joshr120/open-deck/Code/Arduino/macro_keyboard_with_MQTT/bitmap.h

//Custom Bitmaps:

//Image colours are stored seperatly these are just the bitmaps


unsigned char chrome_r [] = {
  0x00, 0x00, 0x00, 0x00, 0x00, 0x00, 0x00, 
0x00, 0x00, 0x00, 0x00, 0x00, 0x00, 0x00, 
0x00, 0x00, 0x00, 0x00, 0x00, 0x00, 0x00, 
0x00, 0x00, 0x00, 0x00, 0x00, 0x00, 0x00, 
0x00, 0x00, 0x00, 0x00, 0x00, 0x00, 0x00, 
0x00, 0x00, 0x00, 0x00, 0x00, 0x00, 0x00, 
0x00, 0x00, 0x00, 0x00, 0x00, 0x00, 0x00, 
0x00, 0x00, 0x00, 0x00, 0x00, 0x00, 0x00, 
0x00, 0x00, 0x00, 0x00, 0x00, 0x00, 0x00, 
0x00, 0x00, 0x01, 0xfe, 0x00, 0x00, 0x00, 
0x00, 0x00, 0x3f, 0xff, 0xe0, 0x00, 0x00, 
0x00, 0x00, 0xff, 0xff, 0xfc, 0x00, 0x00, 
0x00, 0x03, 0xff, 0xff, 0xfe, 0x00, 0x00, 
0x00, 0x0f, 0xff, 0xff, 0xff, 0x80, 0x00, 
0x00, 0x1f, 0xff, 0xff, 0xff, 0xc0, 0x00, 
0x00, 0x3f, 0xff, 0xff, 0xff, 0xf0, 0x00, 
0x00, 0x7f, 0xff, 0xff, 0xff, 0xf8, 0x00, 
0x01, 0xff, 0xff, 0xff, 0xff, 0xfc, 0x00, 
0x01, 0xff, 0xff, 0xff, 0xff, 0xfc, 0x00, 
0x01, 0xff, 0xff, 0xff, 0xff, 0xfe, 0x00, 
0x01, 0xff, 0xff, 0xff, 0xff, 0xff, 0x00, 
0x00, 0xff, 0xff, 0xff, 0xff, 0xff, 0x80, 
0x00, 0x7f, 0xff, 0xff, 0xff, 0xff, 0x80, 
0x00, 0x7f, 0xff, 0xff, 0xff, 0xff, 0x80, 
0x00, 0x3f, 0xfc, 0x00, 0x00, 0x00, 0x00, 
0x00, 0x3f, 0xf0, 0x00, 0x00, 0x00, 0x00, 
0x00, 0x1f, 0xe0, 0x00, 0x00, 0x00, 0x00, 
0x00, 0x0f, 0xc0, 0x00, 0x00, 0x00, 0x00, 
0x00, 0x0f, 0x80, 0x00, 0x00, 0x00, 0x00, 
0x00, 0x07, 0x80, 0x00, 0x00, 0x00, 0x00, 
0x00, 0x07, 0x00, 0x00, 0x00, 0x00, 0x00, 
0x00, 0x03, 0x00, 0x00, 0x00, 0x00, 0x00, 
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
0x00, 0x00, 0x00, 0x00, 0x03, 0xff, 0xf0, 
0x00, 0x00, 0x00, 0x00, 0x03, 0xff, 0xf0, 
0x00, 0x00, 0x00, 0x00, 0x03, 0xff, 0xf0, 
0x00, 0x00, 0x00, 0x00, 0x03, 0xff, 0xf0, 
0x00, 0x00, 0x00, 0x00, 0x03, 0xff, 0xf0, 
0x00, 0x00, 0x00, 0x00, 0x03, 0xff, 0xf0, 
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
};
