joshr120/open-deck/Code/Arduino/macro_keyboard_with_MQTT/home_bitmaps.h

// These arrays are just the default images, uploaded images are stored in SPIFFS.
//Image colours are stored seperatly these are just the bitmaps

//prev page
unsigned char prevPage [] = {
  0x00, 0x00, 0x00, 0x00, 0x00, 0x00, 0x00, 
0x00, 0x00, 0x00, 0x00, 0x00, 0x00, 0x00, 
0x00, 0x00, 0x00, 0x00, 0x00, 0x00, 0x00, 
0x00, 0x00, 0x00, 0x00, 0x00, 0x00, 0x00, 
0x00, 0x00, 0x00, 0x00, 0x00, 0x00, 0x00, 
0x00, 0x00, 0x00, 0x00, 0x00, 0x00, 0x00, 
0x00, 0x00, 0x00, 0x00, 0x00, 0x00, 0x00, 
0x00, 0x00, 0x00, 0x00, 0x00, 0x00, 0x00, 
0x00, 0x00, 0x00, 0x00, 0x00, 0x00, 0x00, 
0x00, 0x00, 0x00, 0x00, 0x00, 0x00, 0x00, 
0x00, 0x00, 0x00, 0x00, 0x00, 0x00, 0x00, 
0x00, 0x00, 0x00, 0x00, 0x00, 0x00, 0x00, 
0x00, 0x00, 0x00, 0x00, 0x00, 0x00, 0x00, 
0x00, 0x00, 0x00, 0x00, 0x00, 0x00, 0x00, 
0x00, 0x00, 0x00, 0x00, 0x00, 0x00, 0x00, 
0x00, 0x00, 0x0e, 0x00, 0x00, 0x00, 0x00, 
0x00, 0x00, 0x1f, 0x00, 0x00, 0x00, 0x00, 
0x00, 0x00, 0x3f, 0x00, 0x00, 0x00, 0x00, 
0x00, 0x00, 0x7f, 0x00, 0x00, 0x00, 0x00, 
0x00, 0x00, 0xff, 0x00, 0x00, 0x00, 0x00, 
0x00, 0x01, 0xfe, 0x00, 0x00, 0x00, 0x00, 
0x00, 0x03, 0xfc, 0x00, 0x00, 0x00, 0x00, 
0x00, 0x07, 0xf8, 0x00, 0x00, 0x00, 0x00, 
0x00, 0x0f, 0xf0, 0x00, 0x00, 0x00, 0x00, 
0x00, 0x1f, 0xe0, 0x00, 0x00, 0x00, 0x00, 
0x00, 0x3f, 0xc0, 0x00, 0x00, 0x00, 0x00, 
0x00, 0x7f, 0x80, 0x00, 0x00, 0x00, 0x00, 
0x00, 0xff, 0x00, 0x00, 0x00, 0x00, 0x00, 
0x01, 0xfe, 0x00, 0x00, 0x00, 0x00, 0x00, 
0x03, 0xfc, 0x00, 0x00, 0x00, 0x00, 0x00, 
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
0x00, 0x00, 0x00, 0x1f, 0xc0, 0x00, 0x00,
0x00, 0x00, 0x00, 0x3f, 0x80, 0x00, 0x00, 
0x00, 0x00, 0x00, 0x3f, 0x80, 0x00, 0x00,
0x00, 0x00, 0x00, 0x7f, 0x00, 0x00, 0x00,
0x00, 0x00, 0x00, 0x7e, 0x00, 0x00, 0x00,
0x00, 0x00, 0x00, 0xfe, 0x00, 0x00, 0x00,
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
}};
  
