joshr120/open-deck/Code/Arduino/macro_keyboard_with_MQTT/menu_bitmaps.h

// These arrays are just the default images, uploaded images are stored in SPIFFS.
//Image colours are stored seperatly these are just the bitmaps

//Home(back) Icon
unsigned char homeIcon [] = {
  0x00, 0x00, 0x00, 0x00, 0x00, 0x00, 0x00, 
0x00, 0x00, 0x00, 0x00, 0x00, 0x00, 0x00, 
0x00, 0x00, 0x00, 0x00, 0x00, 0x00, 0x00, 
0x00, 0x00, 0x00, 0x00, 0x00, 0x00, 0x00, 
0x00, 0x00, 0x00, 0x00, 0x00, 0x00, 0x00, 
0x00, 0x00, 0x00, 0x00, 0x00, 0x00, 0x00, 
0x00, 0x00, 0x00, 0x00, 0x00, 0x00, 0x00, 
0x00, 0x00, 0x00, 0x00, 0x00, 0x00, 0x00, 
0x00, 0x00, 0x00, 0x00, 0x00, 0x00, 0x00, 
0x00, 0x00, 0x00, 0x00, 0x00, 0x00, 0x00, 
0x00, 0x00, 0x00, 0x00, 0x00, 0x00, 0x00, 
0x00, 0x00, 0x00, 0x00, 0x00, 0x00, 0x00, 
0x00, 0x00, 0x00, 0x00, 0x00, 0x00, 0x00, 
0x00, 0x00, 0x00, 0x00, 0x00, 0x00, 0x00, 
0x00, 0x00, 0x00, 0x00, 0x00, 0x00, 0x00, 
0x00, 0x00, 0x00, 0x78, 0x03, 0xf8, 0x00, 
0x00, 0x00, 0x01, 0xfe, 0x07, 0xfc, 0x00, 
0x00, 0x00, 0x03, 0xff, 0x07, 0xfc, 0x00, 
0x00, 0x00, 0x07, 0xff, 0x87, 0xfc, 0x00, 
0x00, 0x00, 0x0f, 0xff, 0xc7, 0xfc, 0x00, 
0x00, 0x00, 0x1f, 0xff, 0xe7, 0xfc, 0x00, 
0x00, 0x00, 0x3f, 0xc7, 0xf7, 0xfc, 0x00, 
0x00, 0x00, 0xff, 0x03, 0xff, 0xfc, 0x00, 
0x00, 0x01, 0xfe, 0x01, 0xff, 0xfc, 0x00, 
0x00, 0x03, 0xfc, 0x78, 0xff, 0xfc, 0x00, 
0x00, 0x07, 0xf8, 0xfc, 0x7f, 0xfc, 0x00, 
0x00, 0x0f, 0xf1, 0xfe, 0x1f, 0xfc, 0x00, 
0x00, 0x3f, 0xc3, 0xff, 0x0f, 0xfc, 0x00, 
0x00, 0x7f, 0x87, 0xff, 0xc7, 0xfc, 0x00, 
0x00, 0xff, 0x1f, 0xff, 0xe3, 0xfc, 0x00, 
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
0x00, 0x01, 0xf8, 0x01, 0xff, 0x00, 0x00,
0x00, 0x01, 0xf8, 0x03, 0xff, 0x00, 0x00,
0x00, 0x01, 0xf8, 0x03, 0xff, 0x80, 0x00,
0x00, 0x01, 0xf8, 0x07, 0xcf, 0x80, 0x00,
0x00, 0x01, 0xf8, 0x07, 0xc7, 0x80, 0x00,
0x00, 0x00, 0x78, 0x03, 0xcf, 0x80, 0x00,
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
},
};
